dlin7195/Micromouse-20-21/irs.c

/*
 * irs.c
 *
 *  Template created on: Sep 29, 2020
 *      Author: Bradley Schulz
 */

#include "main.h"
#include "irs.h"
#include "delay.h"

// buffer that will get filled up with all the measurements
uint16_t adc_buf[NUM_SAMPLES];
// "boolean" variable to keep say when the ADC has finished filling up the buffer
uint8_t complete = 0;


/*
 function for handling everything for reading a specific IR
 1. turn on the correct IR emitter
 2. Wait for a small amount of time (at least 20 us) so the photodiode can react
 3. Then read the correct receiver
 4. Lastly turn off the emitter
 */
uint16_t readIR(IR ir)
{
   // try flipping diode if this doesn't work
	switch(ir)
	{
		case IR_LEFT:
			HAL_GPIO_WritePin(LeftEmitter_GPIO_Port, LeftEmitter_Pin, GPIO_PIN_SET);
			break;
		case IR_FRONT:
			HAL_GPIO_WritePin(GPIOA, FrontEmitter_Pin, GPIO_PIN_SET);
			break;
		case IR_RIGHT:
			HAL_GPIO_WritePin(GPIOA, RightEmitter_Pin, GPIO_PIN_SET);
		    break;
	}
	delayMicroseconds(60);
	uint16_t ir_read = analogRead(ir);

	// Reset all the emitters
	HAL_GPIO_WritePin(LeftEmitter_GPIO_Port, LeftEmitter_Pin, GPIO_PIN_RESET);
	HAL_GPIO_WritePin(GPIOA, FrontEmitter_Pin, GPIO_PIN_RESET);
	HAL_GPIO_WritePin(GPIOA, RightEmitter_Pin, GPIO_PIN_RESET);

	return ir_read;
}

uint16_t readLeftIR(void)
{
	return readIR(IR_LEFT);
}

uint16_t readFrontIR(void)
{
	return readIR(IR_FRONT);
}

uint16_t readRightIR(void)
{
	return readIR(IR_RIGHT);
}

/*
 This function reads the specific channel of the ADC corresponding to the correct IR
*/
uint16_t analogRead(IR ir)
{
    ADC_ChannelConfTypeDef sConfig = {0}; // initializes the IR ADC [Analog to Digital Converter]
    ADC_HandleTypeDef *hadc1_ptr = Get_HADC1_Ptr(); // pointer to your hal_adc
    //this pointer will also be used to read the analog value, val = HAL_ADC_GetValue(hadc1_ptr);

    // picks the IR direction to choose the right ADC.
    switch(ir)
    {
        case IR_LEFT:
            sConfig.Channel = ADC_CHANNEL_15;
            break;
        case IR_FRONT:
            sConfig.Channel = ADC_CHANNEL_7;
            break;
        case IR_RIGHT:
            sConfig.Channel = ADC_CHANNEL_5;
            break;
        default:
            return 0;
    }

    sConfig.Rank = 1;
    sConfig.SamplingTime = ADC_SAMPLETIME_3CYCLES;

    // make sure everything was set up correctly
    if (HAL_ADC_ConfigChannel(hadc1_ptr, &sConfig) != HAL_OK)
    {
        return 0;
    }
    
    complete = 0;

    // start filling up the ADC buffer
    HAL_ADC_Start_DMA(hadc1_ptr, (uint32_t*)adc_buf, NUM_SAMPLES);

    // wait for the buffer to become full
    while (complete == 0)
    {
        continue;
    }

    uint32_t sum = 0;
    // calculate the sum of the measurements in order to calculate the average
    uint16_t measurement = 0;
    while(measurement < NUM_SAMPLES) //this takes multiple measurements
    {
        sum += adc_buf[measurement];
        ++measurement;
    }

    return sum/NUM_SAMPLES;
}

/*
 This function is called when the ADC buffer is filled
 It stops the ADC and changes our "complete" variable to be "true"
 */
void HAL_ADC_ConvCpltCallback(ADC_HandleTypeDef* hadc) {
    // stop the ADC
    HAL_ADC_Stop_DMA(hadc);
    complete = 1;
}
