dlin7195/Micromouse-20-21/systick.h

/*
 * systick.c
 *
 *  Created on: Sep 26, 2020
 *      Author: Tyler Price
 */

#ifndef INC_SYSTICK_H_
#define INC_SYSTICK_H_

#include "main.h"

void SysTickFunction(void);

#endif /* INC_SYSTICK_H_ */
